adorablesoft/gcc-triggermodbrackets/Low Profile Mech Switch/LowProfileMechRight.stl

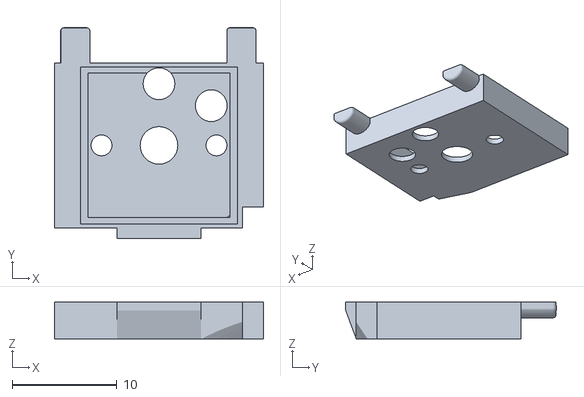
[picture p14: CAD file, 2024-11-06]
Low Profile Mech Switch/LowProfileMechRight.stl
20.0 x 20.2 x 3.50
